boda-akos/STM32-Voltmeter-Data-Logger-Calculator/diodes.png

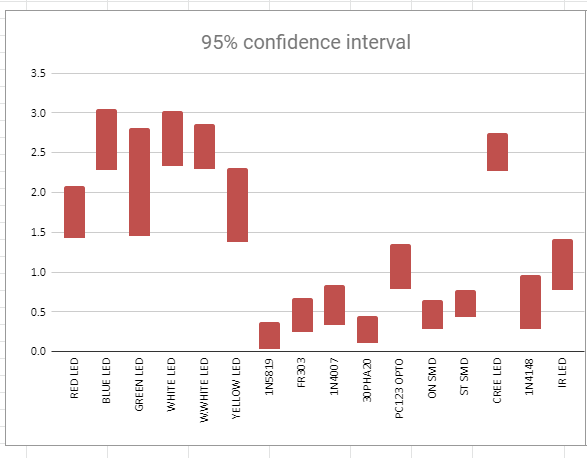
diodes.png
