boda-akos/STM32-Voltmeter-Data-Logger-Calculator/DSCF2548 (Nagy).jpg

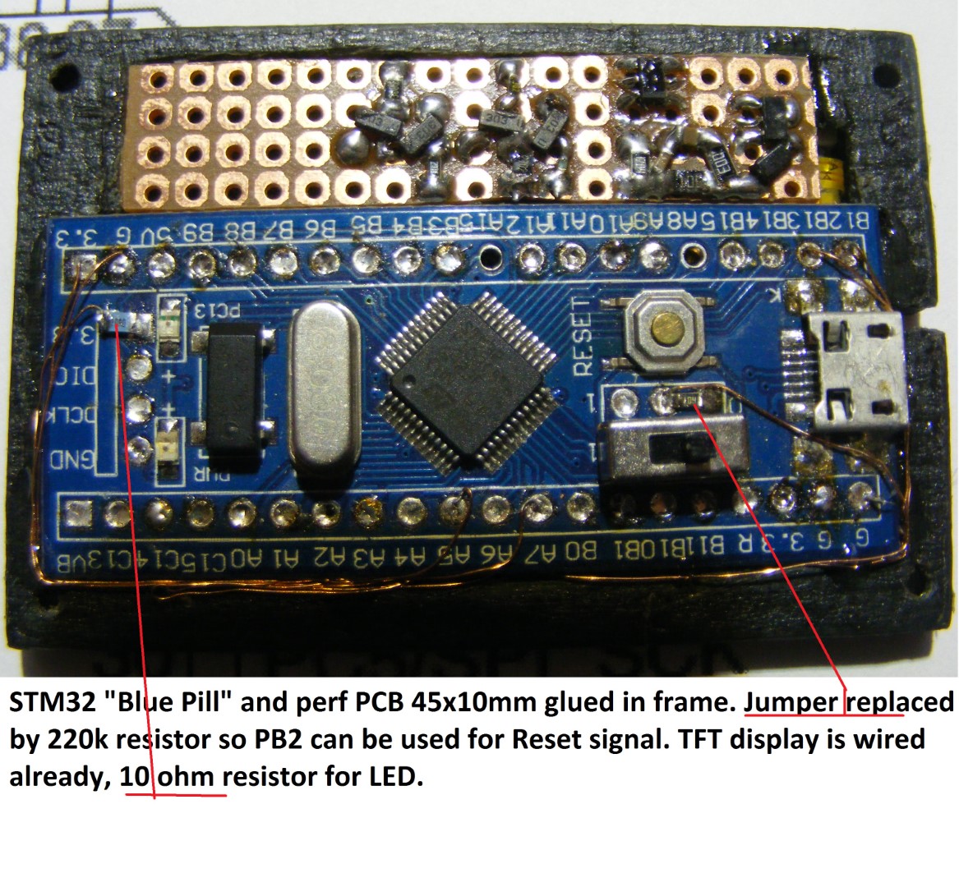
DSCF2548 (Nagy).jpg
