boda-akos/STM32-Voltmeter-Data-Logger-Calculator/DSCF2551 (Nagy).JPG

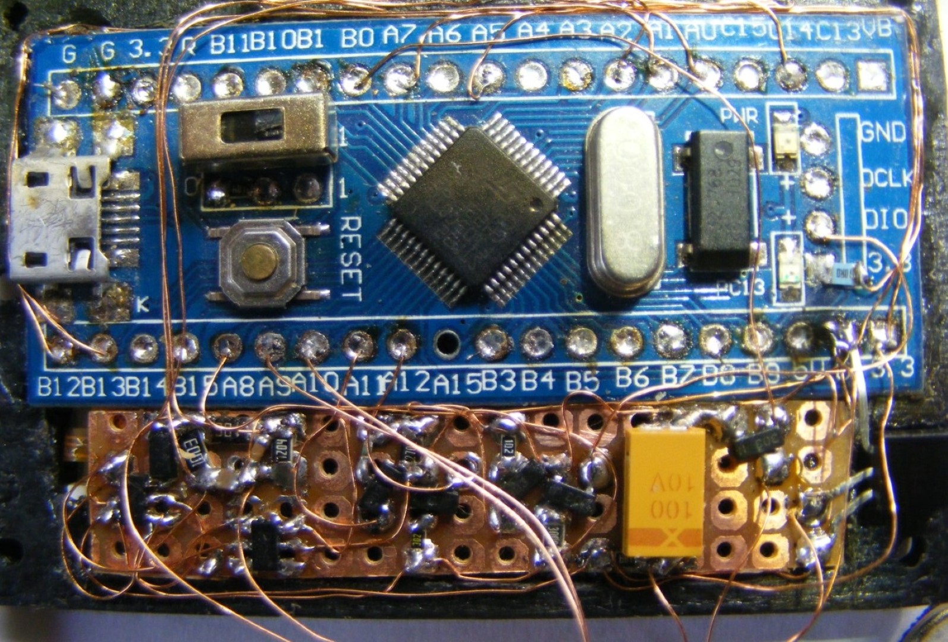
DSCF2551 (Nagy).JPG
