boda-akos/STM32-Voltmeter-Data-Logger-Calculator/DSCF2552 (Nagy).JPG

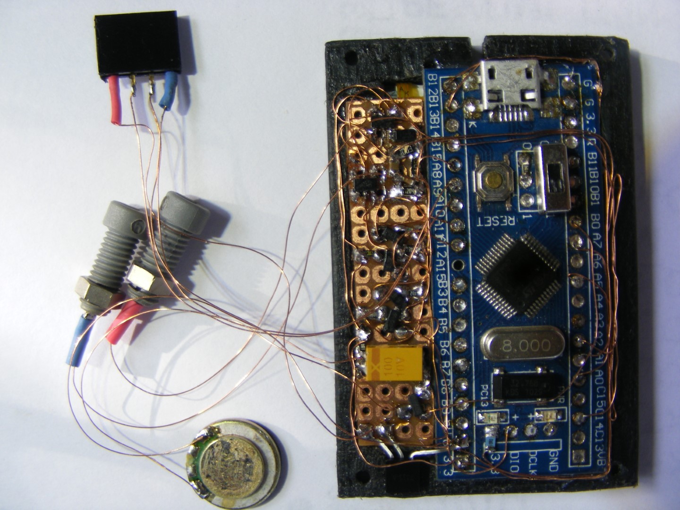
DSCF2552 (Nagy).JPG
