boda-akos/STM32-Voltmeter-Data-Logger-Calculator/DSCF2555 (Nagy).JPG

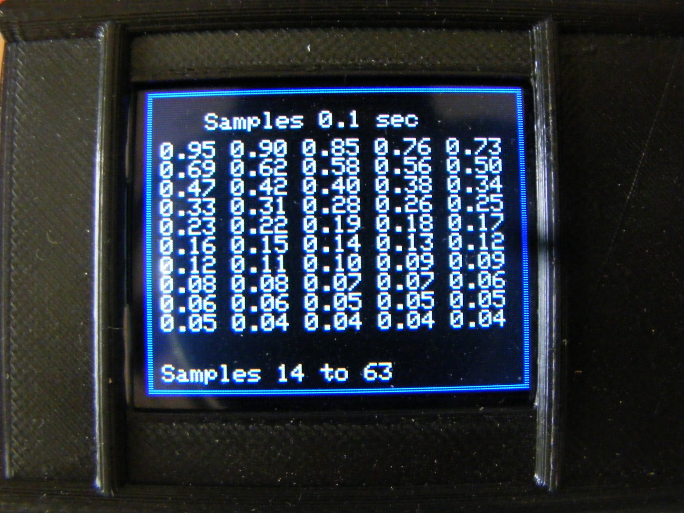
DSCF2555 (Nagy).JPG
