boda-akos/STM32-Voltmeter-Data-Logger-Calculator/DSCF2562 (Nagy).JPG

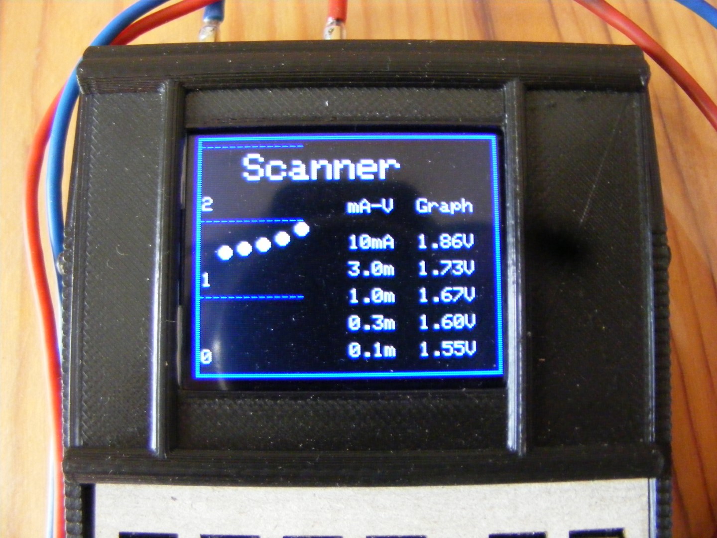
DSCF2562 (Nagy).JPG
