boda-akos/STM32-Voltmeter-Data-Logger-Calculator/DSCF2563 (Nagy).JPG

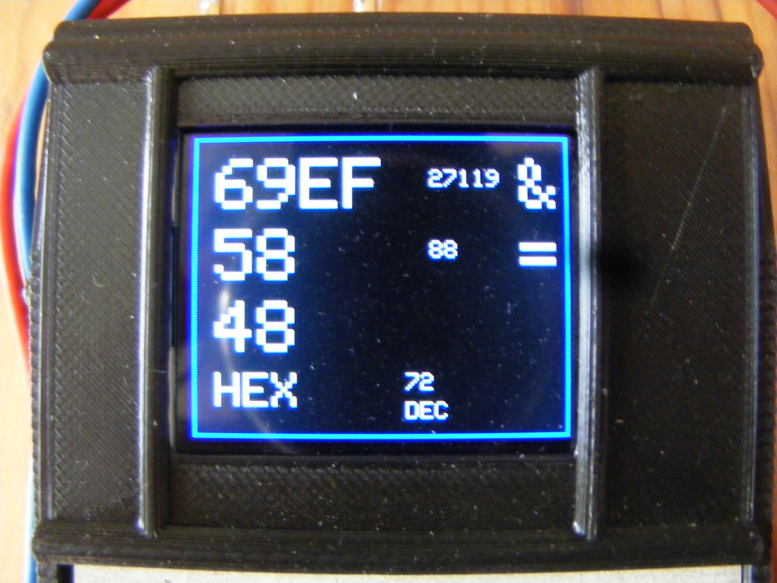
DSCF2563 (Nagy).JPG
