boda-akos/STM32-Voltmeter-Data-Logger-Calculator/DSCF2564 (Nagy).JPG

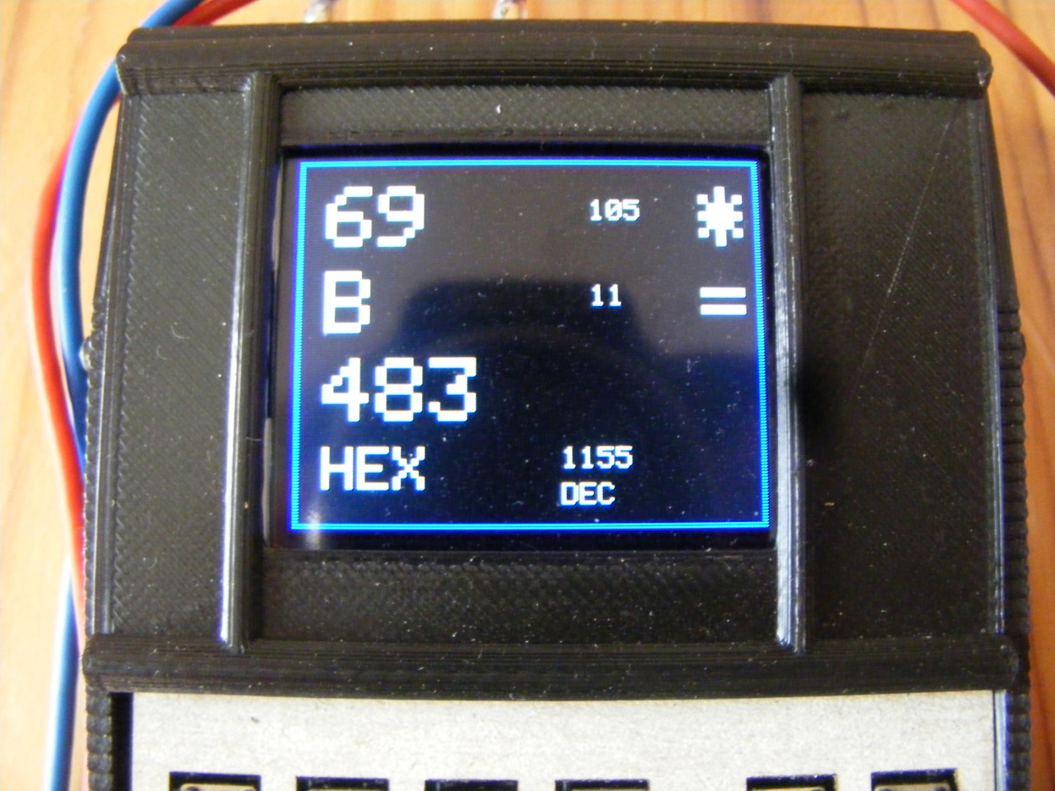
DSCF2564 (Nagy).JPG
