boda-akos/STM32-Voltmeter-Data-Logger-Calculator/hexCalc.png

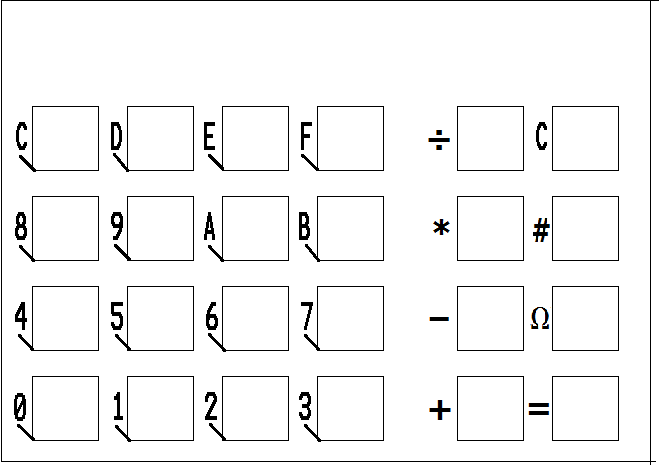
hexCalc.png
