boda-akos/STM32-Voltmeter-Data-Logger-Calculator/sch.png

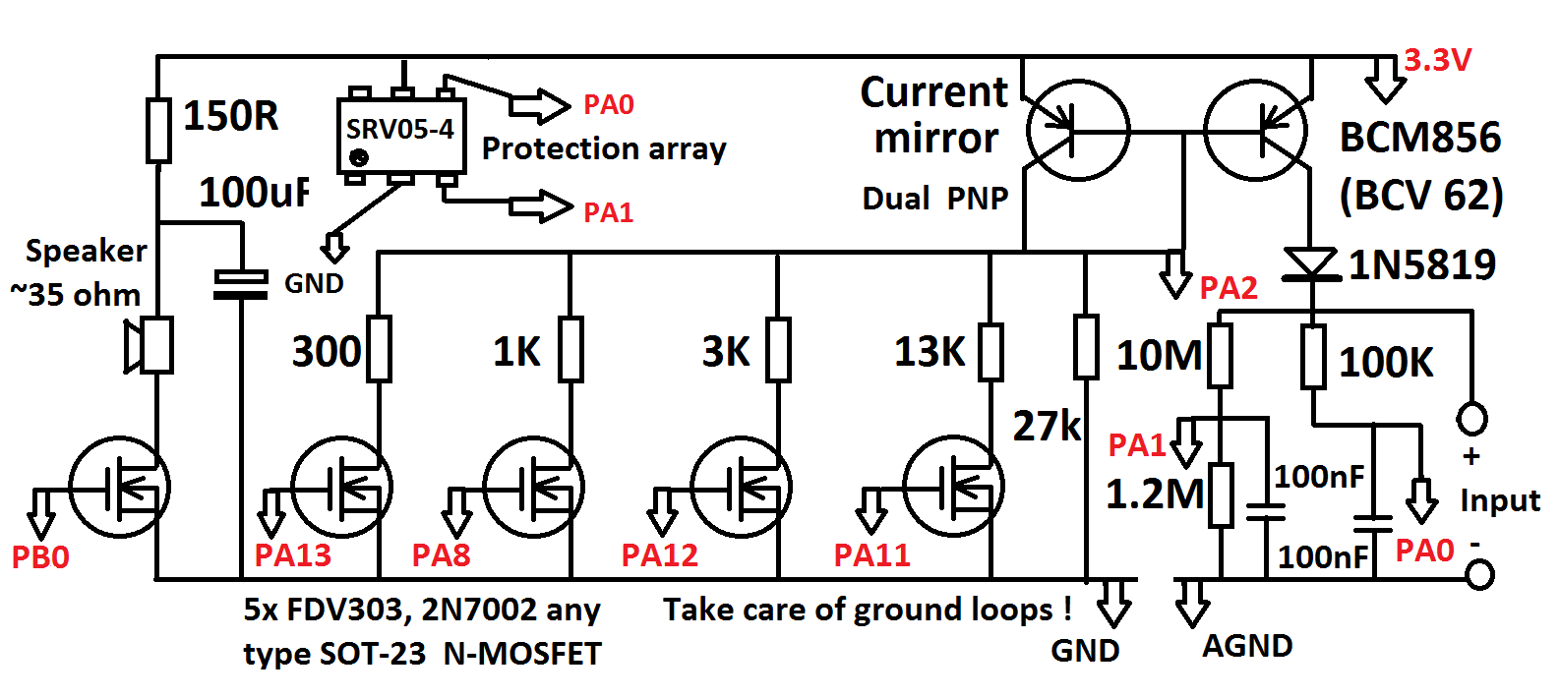
sch.png
