boda-akos/STM32-Voltmeter-Data-Logger-Calculator/switchMatrix.png

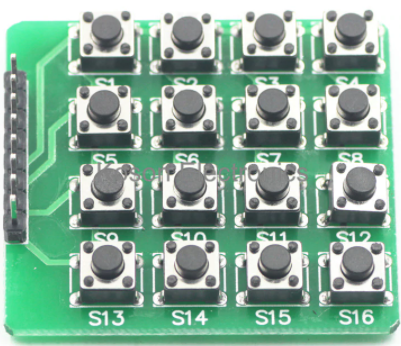
switchMatrix.png
